jzkmath/AMP-Lab-Modular-Synth/KiCAD/MIDI Controller/MIDI Controller BOM.xlsx

Item | Qty | Reference(s) | Value | Footprint | Cost ea | Total Cost | Digikey | Link | Final Cost: | $88.60
1 | 25 | C1, C2, C6, C10-C15, C19-C22, C25-C36 | 0.1uF | SMD 1206 | $0.24 | $5.92 | 720-1540-1-ND | https://www.digikey.com/short/p4zvzf
2 | 10 | C3, C5, C7-C9, C16-C18, C23, C24 | 1uF | SMD 1206 | $0.16 | $1.56 | 399-1254-1-ND | https://www.digikey.com/short/p4zv9n
3 | 1 | C4 | 4.7uF | SMD 1206 | $0.27 | $0.27 | 399-1262-1-ND | https://www.digikey.com/short/p4zvbc
4 | 1 | D1 | 1N914 | THT | $0.10 | $0.10 | 1N914FS-ND | https://www.digikey.com/short/p4zvb4
5 | 1 | J1 | 2040002-1 | USB | $2.40 | $2.40 | A108263CT-ND | https://www.digikey.com/short/p4zvb1
6 | 1 | J2 | Power | 2x5 Header | $0.28 | $0.28 | 609-3243-ND | https://www.digikey.com/short/pzbbv4
7 | 1 | J3 | MIDI | DIN 5 | $3.17 | $3.17 | CP-1250-ND | https://www.digikey.com/short/p4zv2w
8 | 1 | J4 | Prog Jumper | 1x2 Header | $0.13 | $0.13 | 732-5315-ND | https://www.digikey.com/short/p4zvrd
9 | 13 | J5-J17 | HP Jack | External | $1.50 | $19.50 | 486-3418-ND | https://www.digikey.com/short/pzbbdf
10 | 3 | R1-R3 | 1k | SMD 1206 | $0.10 | $0.30 | 311-1.0KERCT-ND | https://www.digikey.com/short/pzbr9h
11 | 2 | R4, R6 | 220 ohm | SMD 1206 | $0.10 | $0.20 | 311-220FRCT-ND | https://www.digikey.com/short/p4zv97
12 | 1 | R5 | 4.7k | SMD 1206 | $0.10 | $0.10 | A130181CT-ND | https://www.digikey.com/short/pzbrh2
13 | 1 | U1 | ATmega328PB-AU | SMD TQFP-32 | $2.14 | $2.14 | ATMEGA328P-AURCT-ND | https://www.digikey.com/short/p4zv43
14 | 1 | U2 | FT232RL | SMD SSOP-28 | $4.50 | $4.50 | 768-1007-1-ND | https://www.digikey.com/short/p4zv5z
15 | 7 | U3-U5, U7-U10 | AD5293 | SMD TSSOP-14 | $6.22 | $43.53 | AD5293BRUZ-100-RL7CT-ND | https://www.digikey.com/short/p4zv5w
16 | 1 | U6 | LM1117-5.0 | SOT 23 | $1.14 | $1.14 | LM1117MP-5.0/NOPBCT-ND | https://www.digikey.com/short/p4zv51
17 | 1 | U11 | 6N138 | DIP 8 | $0.81 | $0.81 | 160-1795-ND | https://www.digikey.com/short/p4zvrz
18 | 4 | U12-U15 | TL074 | SOIC-14 | $0.51 | $2.04 | 296-1283-1-ND | https://www.digikey.com/short/pzz2fn
19 | 1 | Y1 | 16 MHz | XTAL | $0.41 | $0.41 | 535-9362-1-ND | https://www.digikey.com/short/p4zv4h
20 | 1 | N/A | Jumper Conn | N/A | $0.10 | $0.10 | S9337-ND | https://www.digikey.com/short/p4zvfq
 |  |  |  |  |  | $0.00
 |  |  |  |  |  | $0.00
 |  |  |  |  |  | $0.00
 |  |  |  |  |  | $0.00
 |  |  |  |  |  | $0.00
 |  |  |  |  |  | $0.00
 |  |  |  |  |  | $0.00
 |  |  |  |  |  | $0.00
 |  |  |  |  |  | $0.00
 |  |  |  |  |  | $0.00
