jzkmath/AMP-Lab-Modular-Synth/KiCAD/VCA/JZK VCA PCB.pdf

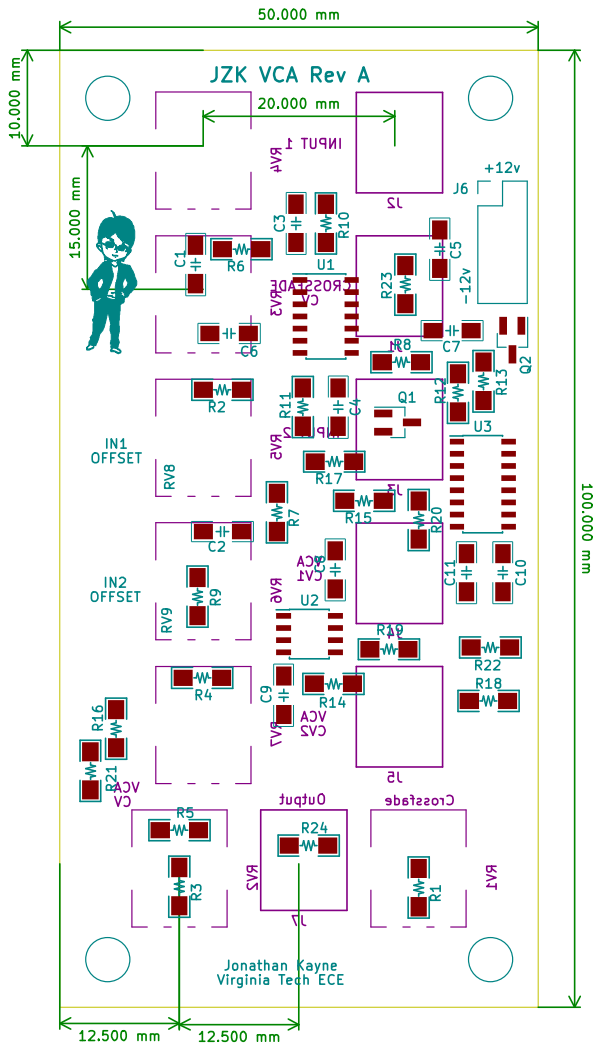
[picture p31: page 1]
