jzkmath/AMP-Lab-Modular-Synth/KiCAD/VCO_2/JZK_VCO.pdf

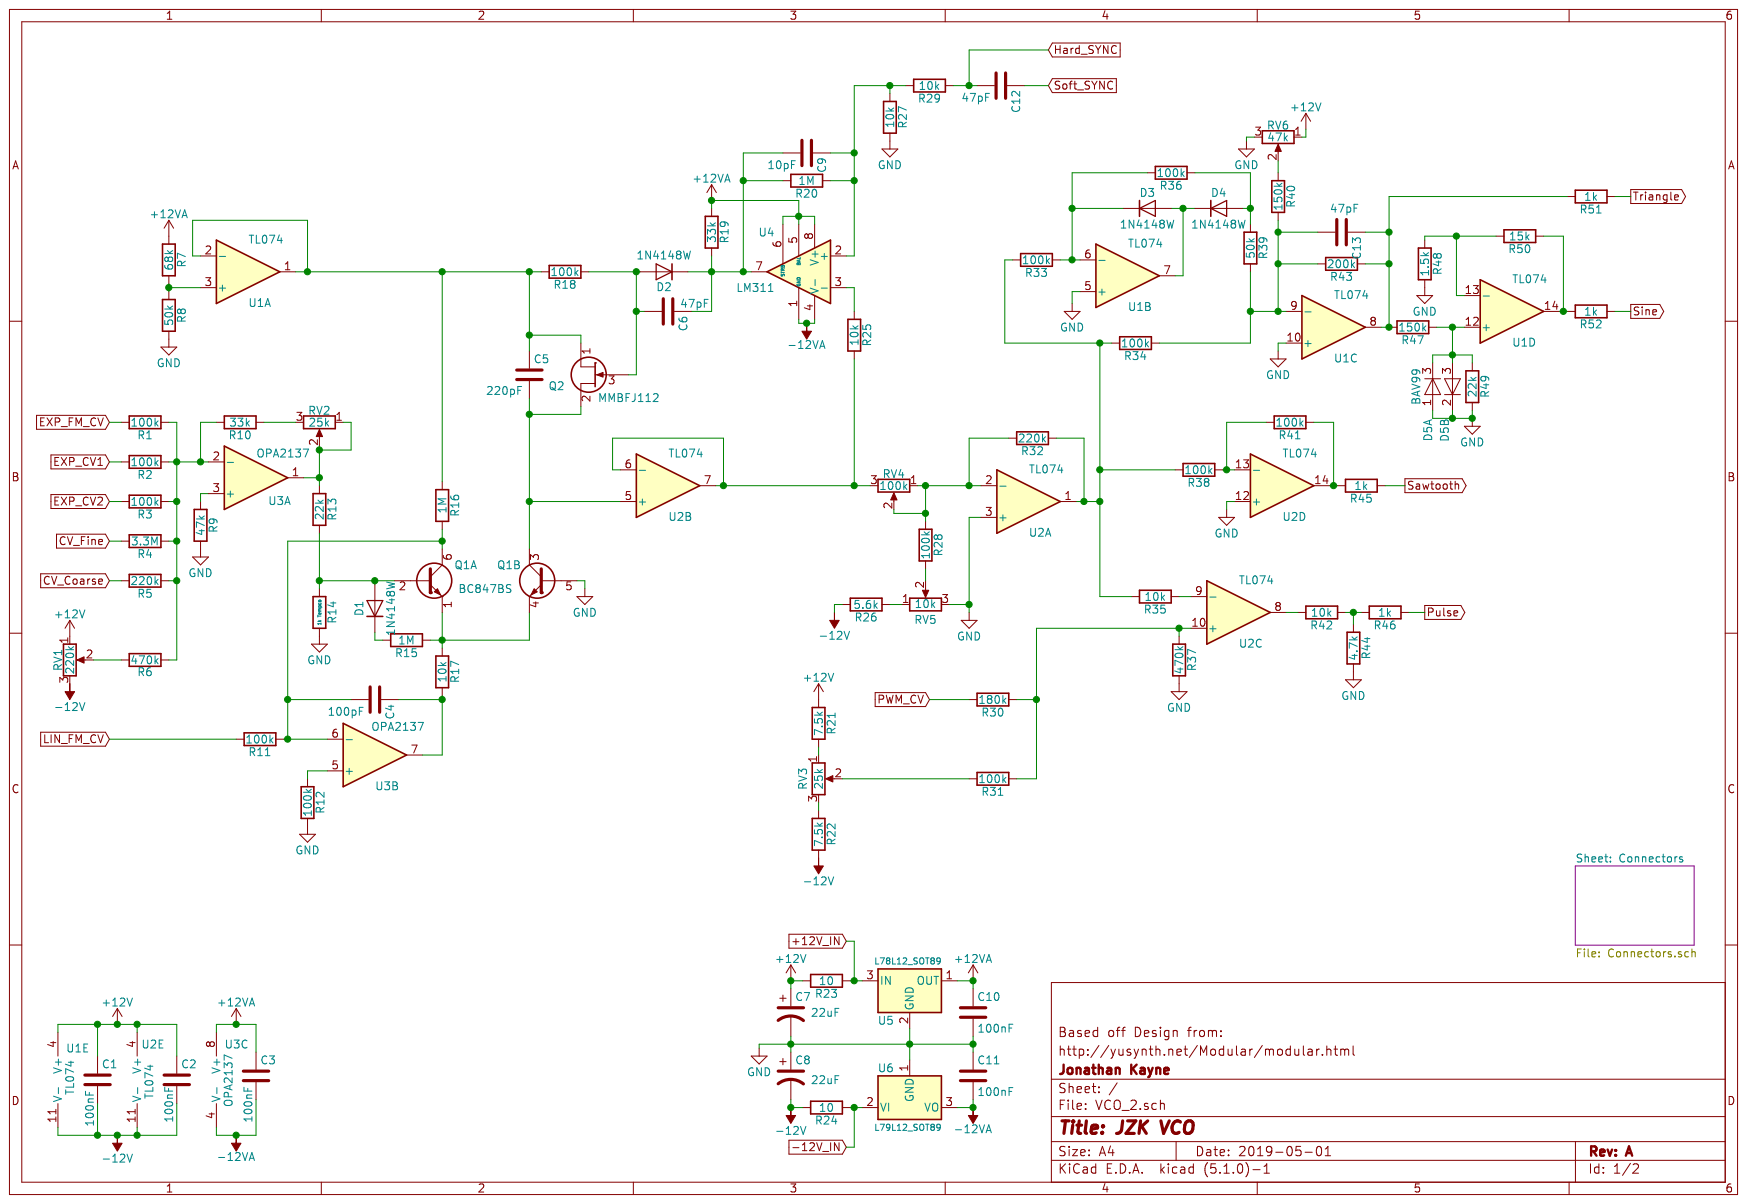
[picture p32: page 1]

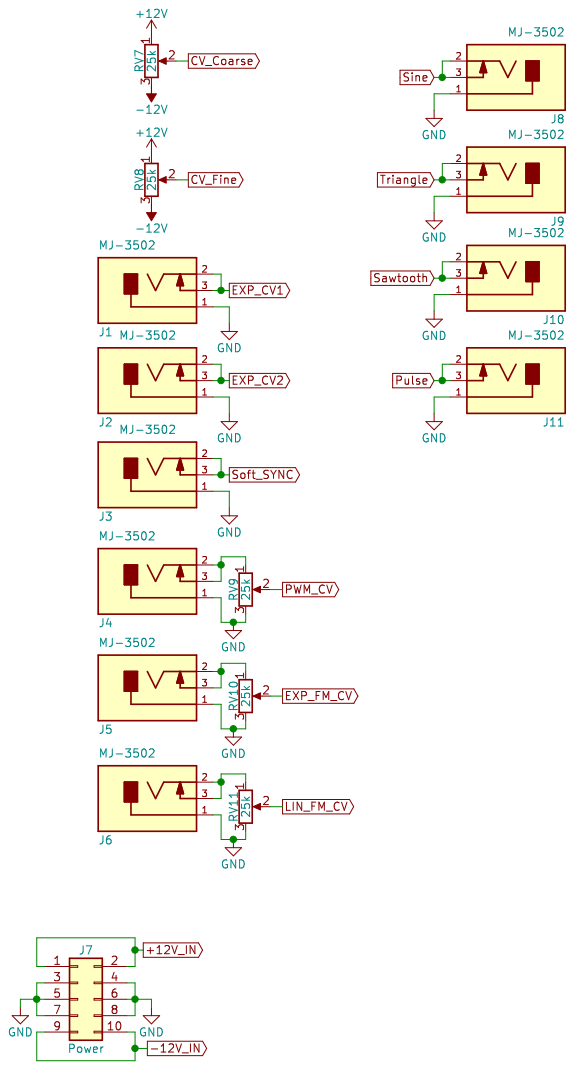
[picture p33: page 2]
